xsrf/Drobo5N/Unit1/Screenshots/2026-05-09 11_09_50-Drobo Dashboard.png

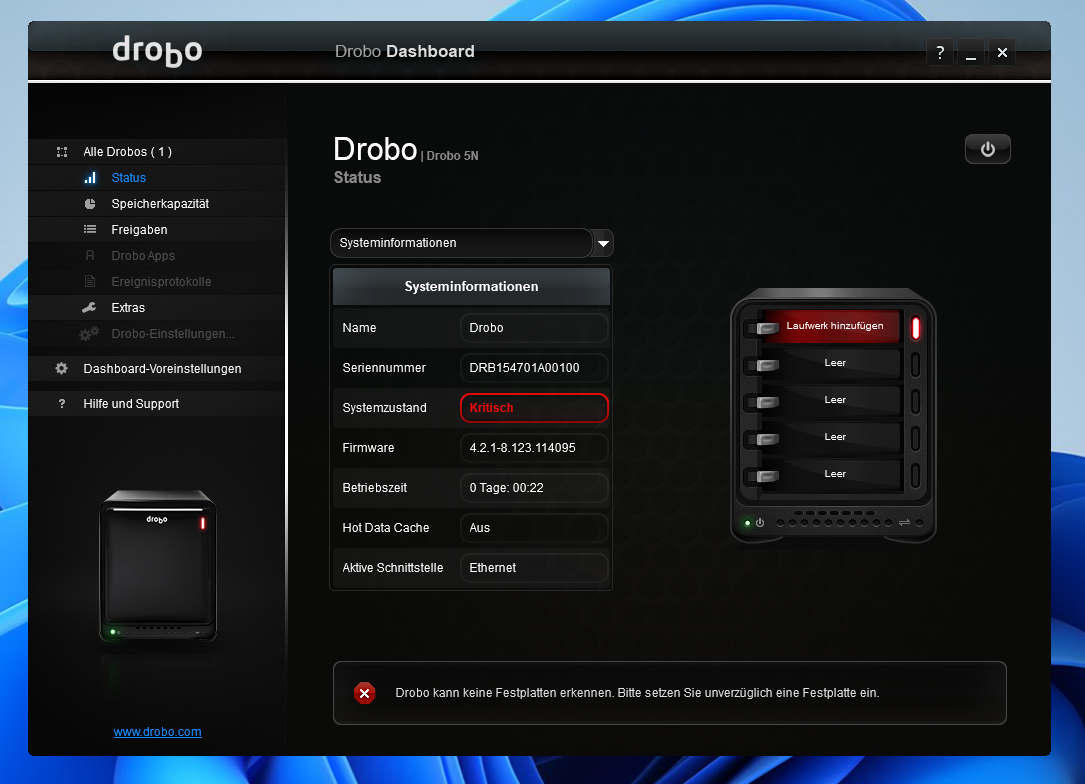
Unit1/Screenshots/2026-05-09 11_09_50-Drobo Dashboard.png
