xsrf/Drobo5N/Unit1/Screenshots/2026-05-09 11_10_34-Drobo Dashboard.png

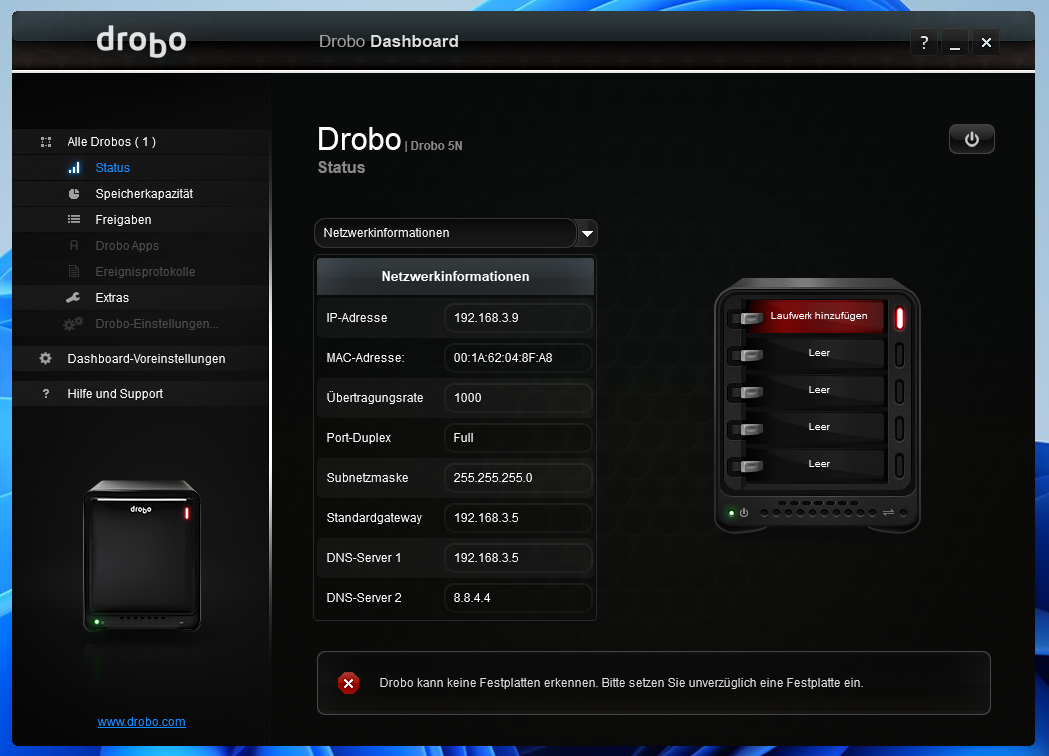
Unit1/Screenshots/2026-05-09 11_10_34-Drobo Dashboard.png
